tidus747/Adap_multicamara_NJTX2/Array_captures/Scene_5/CAM4_playmobil.jpg

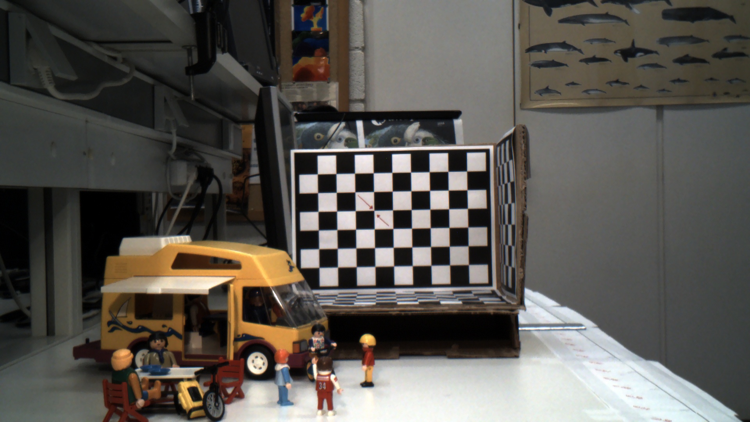
Array_captures/Scene_5/CAM4_playmobil.jpg
