tidus747/Adap_multicamara_NJTX2/Array_captures/Scene_5/Estereo.png

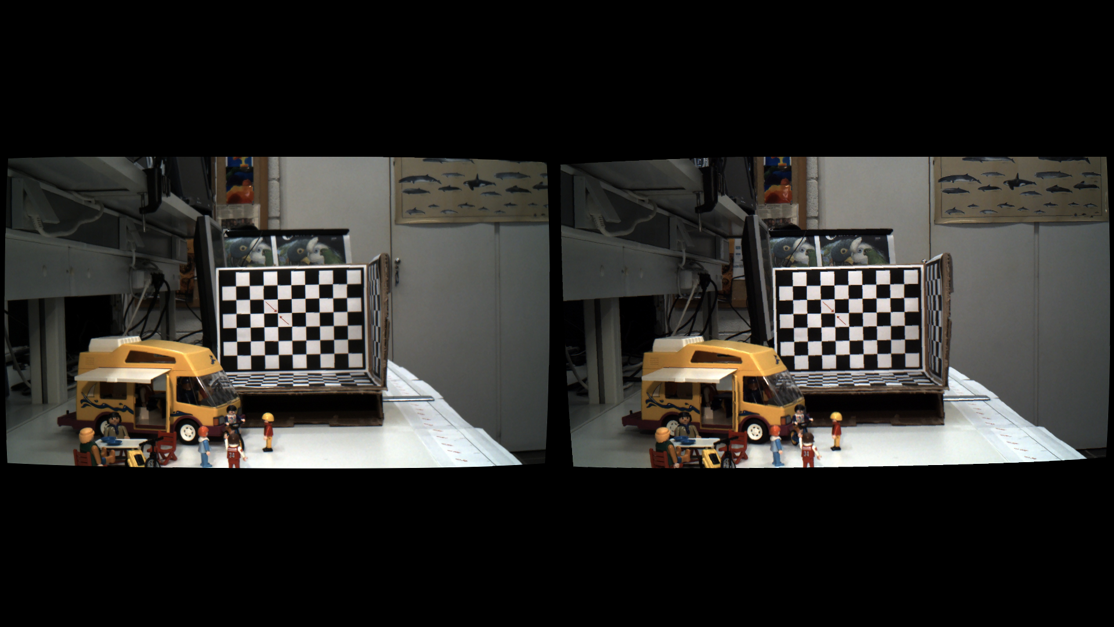
Array_captures/Scene_5/Estereo.png
