tidus747/Adap_multicamara_NJTX2/Array_captures/Scene_6/CAM0_playmobil-2.jpg

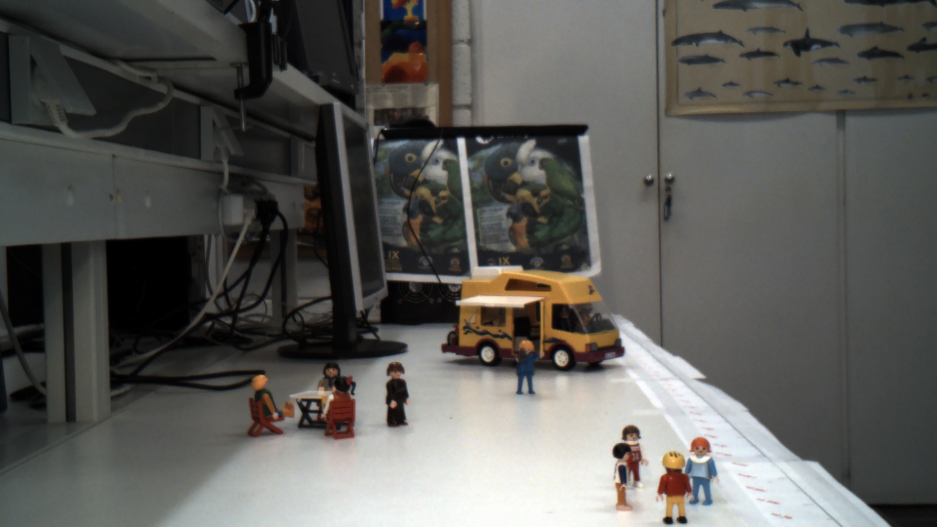
Array_captures/Scene_6/CAM0_playmobil-2.jpg
