tidus747/Adap_multicamara_NJTX2/Array_captures/Scene_8/CAM0_spiderman.jpg

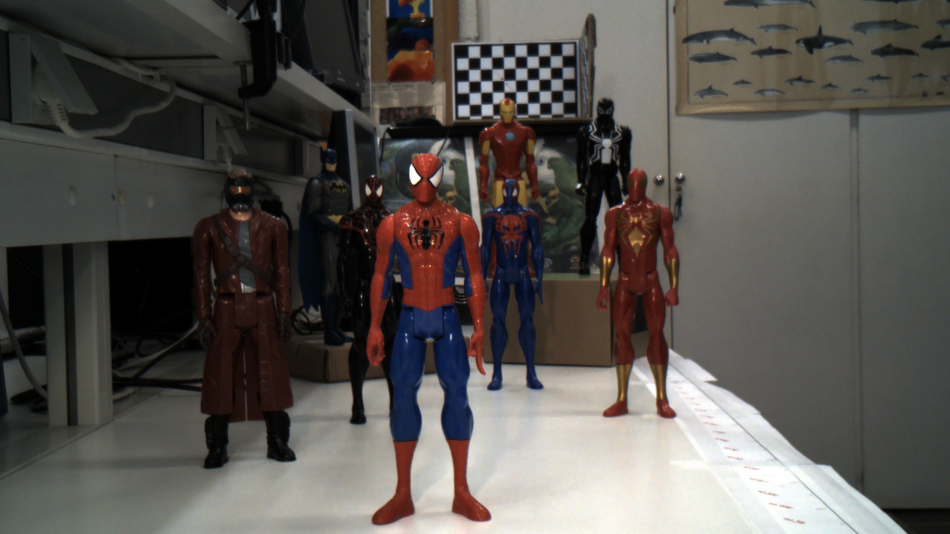
Array_captures/Scene_8/CAM0_spiderman.jpg
