tidus747/Adap_multicamara_NJTX2/Array_captures/Scene_8/CAM3_spiderman.jpg

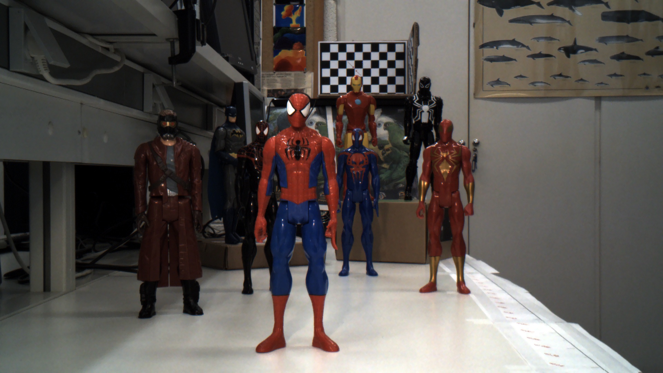
Array_captures/Scene_8/CAM3_spiderman.jpg
