tidus747/Adap_multicamara_NJTX2/Array_captures/Scene_9/CAM0_spiderman-2.jpg

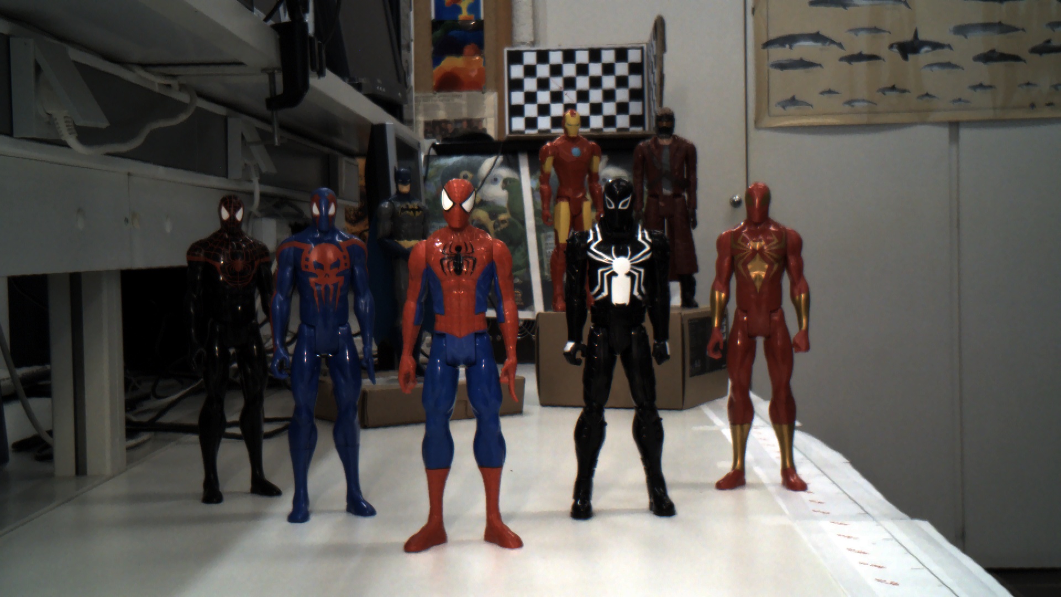
Array_captures/Scene_9/CAM0_spiderman-2.jpg
