tidus747/Adap_multicamara_NJTX2/Desarrollo_Software/Camera_array/Capture_Gstreamer/rejilla.png

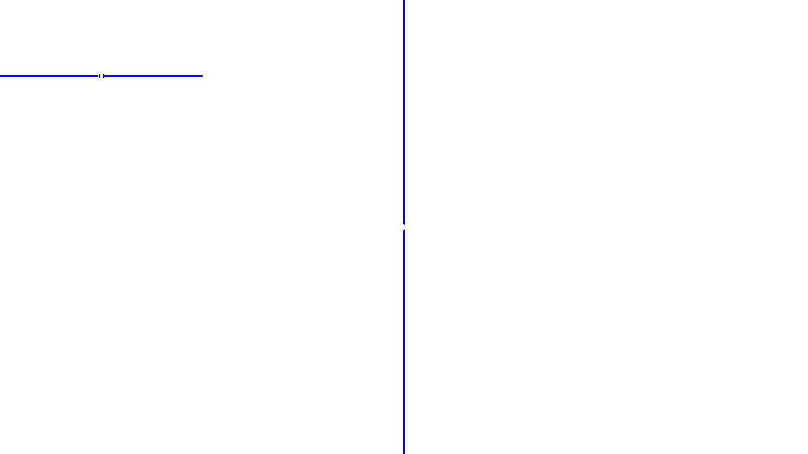
Desarrollo_Software/Camera_array/Capture_Gstreamer/rejilla.png
