tidus747/Adap_multicamara_NJTX2/Desarrollo_Mecanico/Array /Versión V1.1/N10.pdf

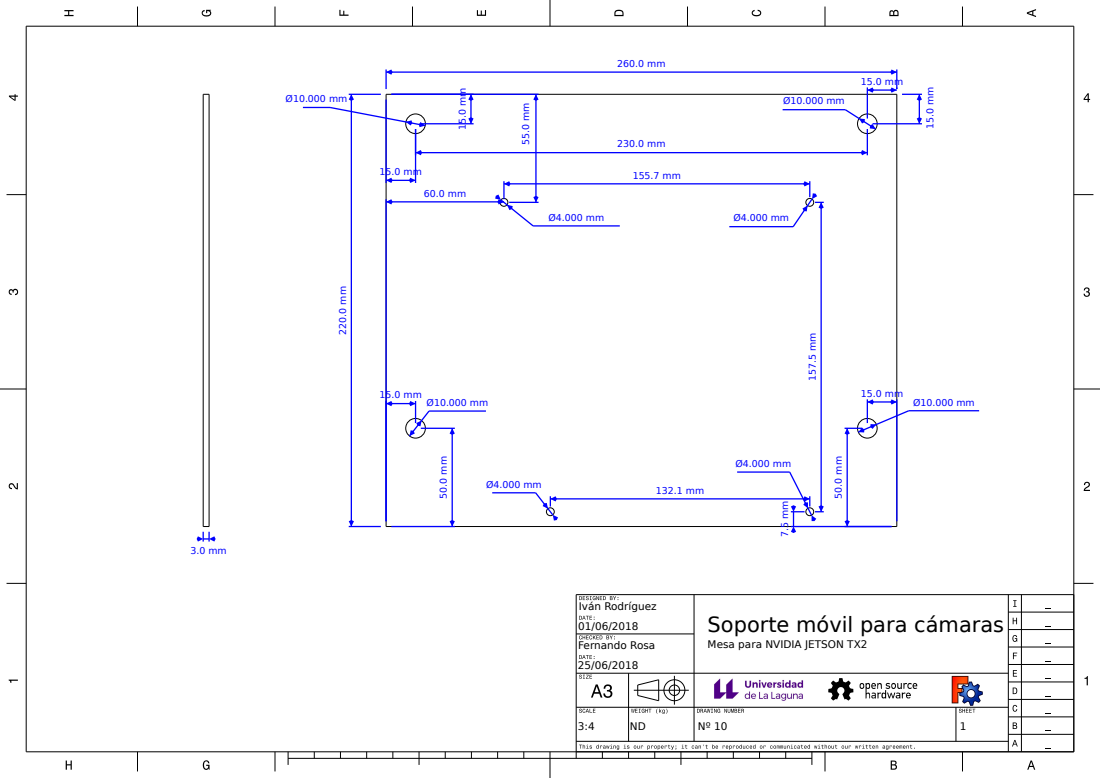
[picture p39: page 1]
Iván Rodríguez; Fernando Rosa

Soporte móvil para cámaras

Mesa para NVIDIA JETSON TX2
