tidus747/Adap_multicamara_NJTX2/Desarrollo_Electronico/Modulo_puente_Raspberry_Camera/Fabricación/Puente_OV5680X1-F.Cu.pdf

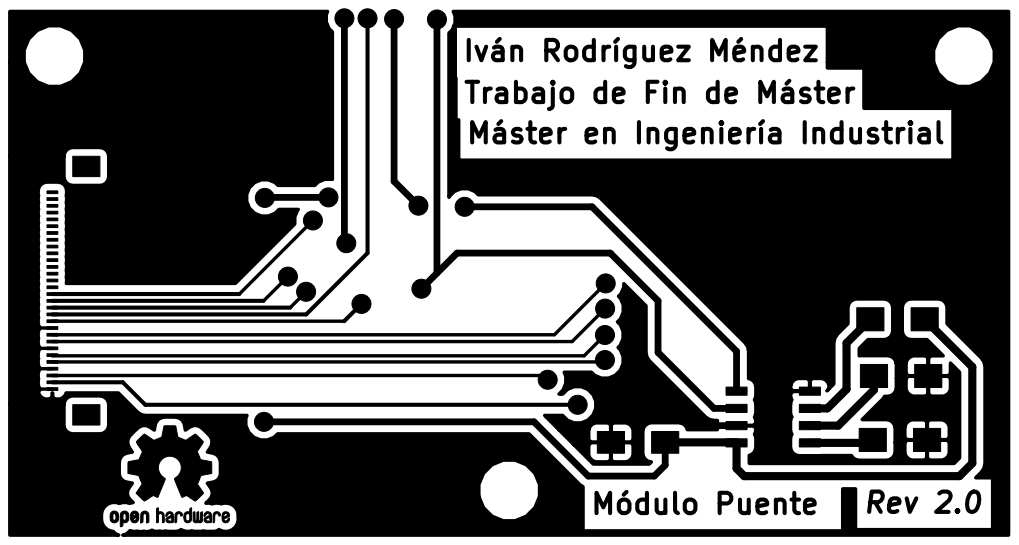
[picture p58: page 1]
