tidus747/Adap_multicamara_NJTX2/Desarrollo_Electronico/Modulo_puente_Raspberry_Camera/PDFs/ACIDO-PUENTE.pdf

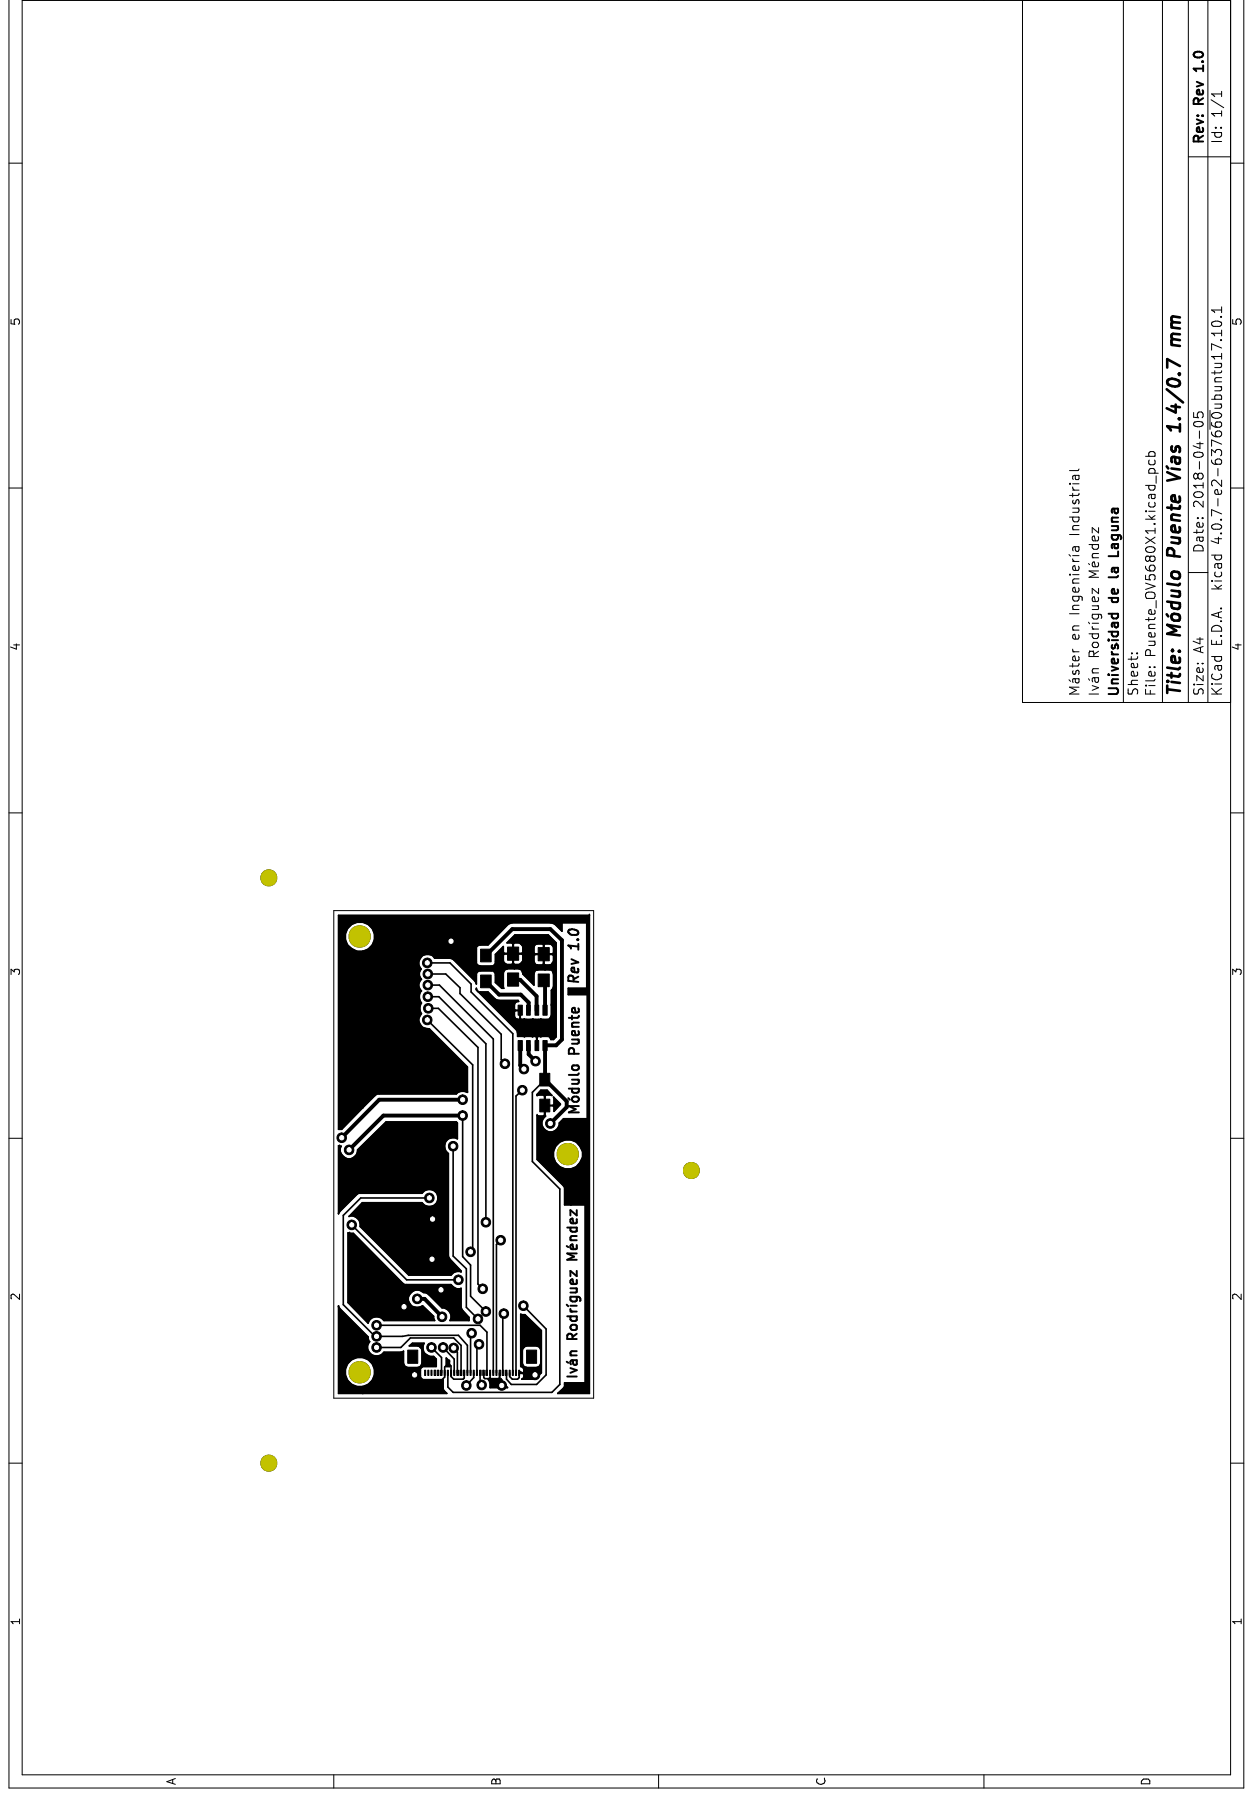
[picture p59: page 1]

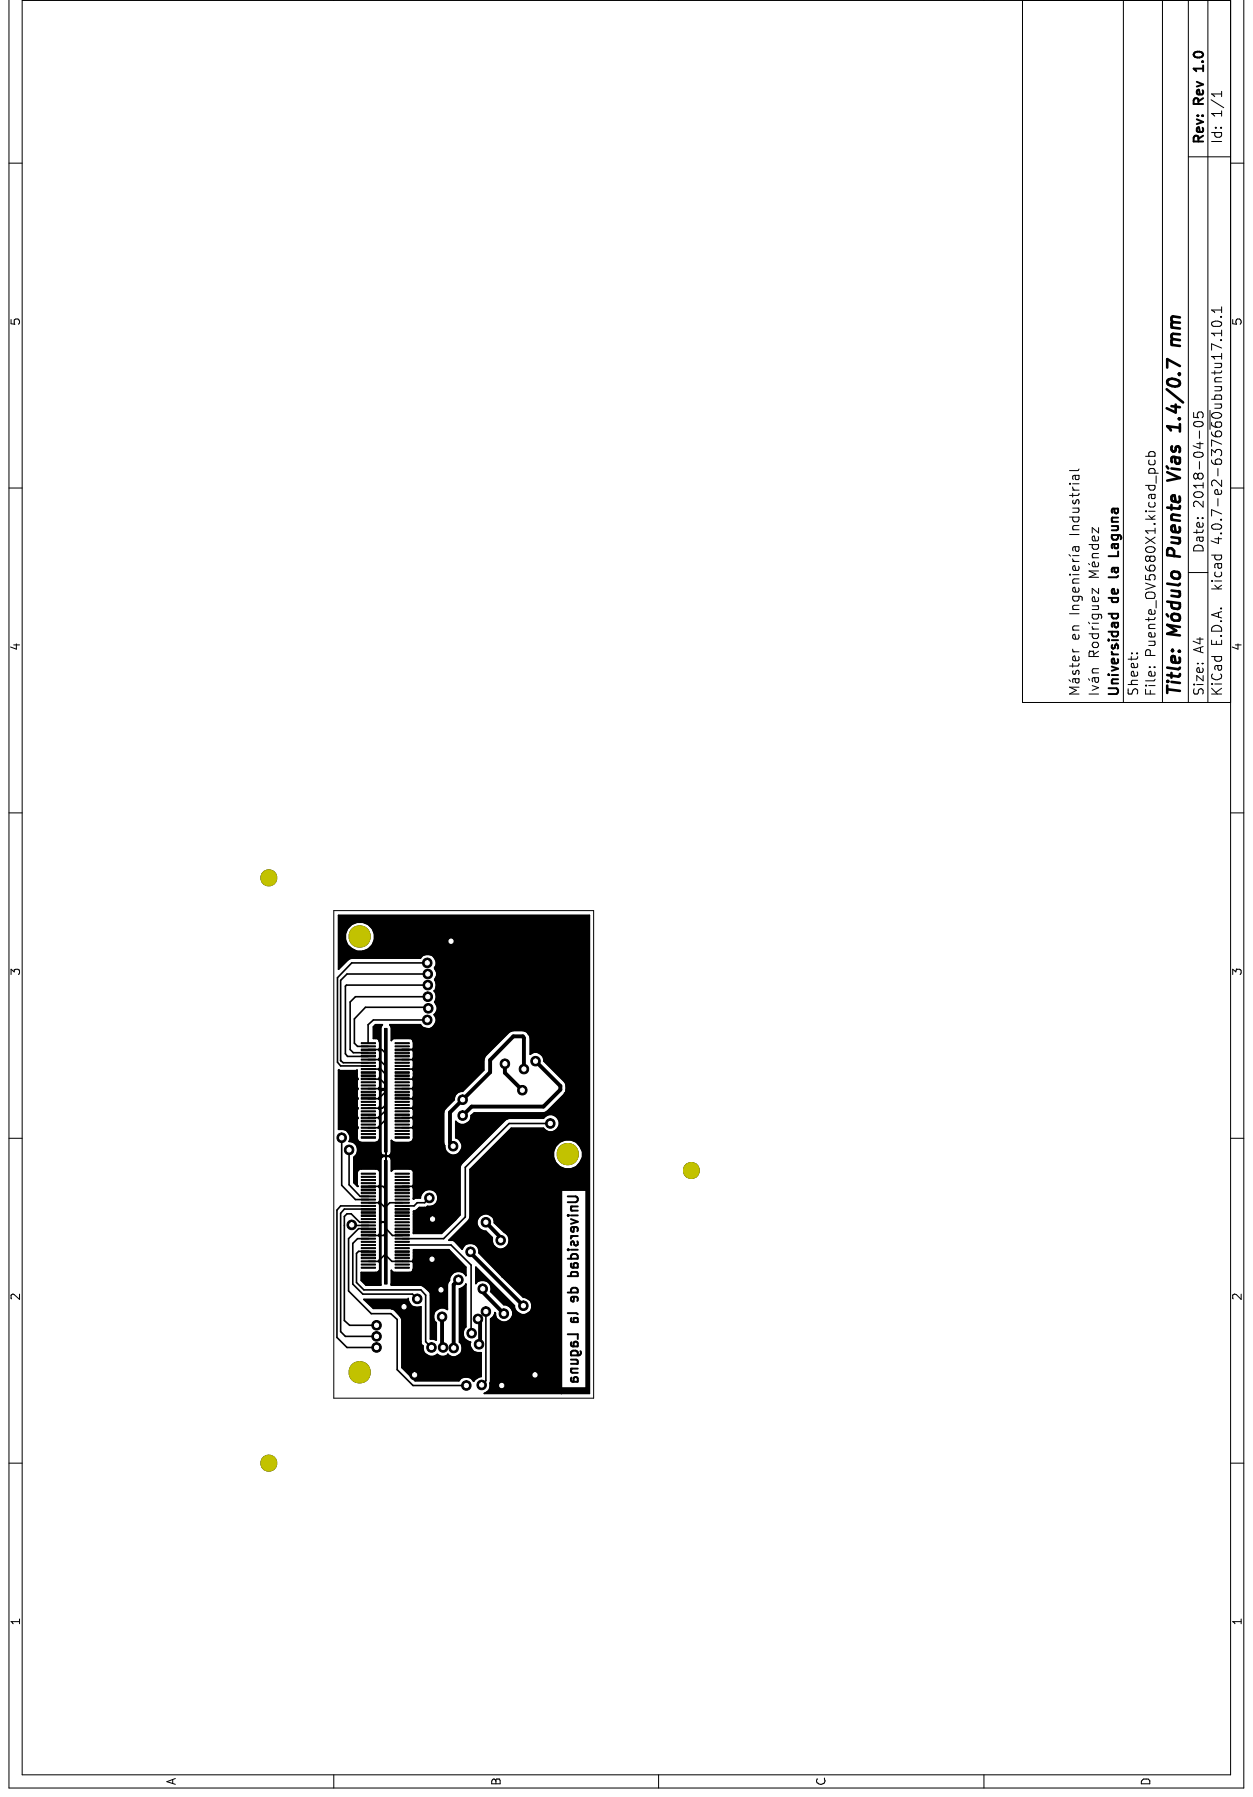
[picture p60: page 2]
