tidus747/Adap_multicamara_NJTX2/Desarrollo_Electronico/Modulo_puente_Raspberry_Camera/PDFs/ACIDO_PUENTE.pdf

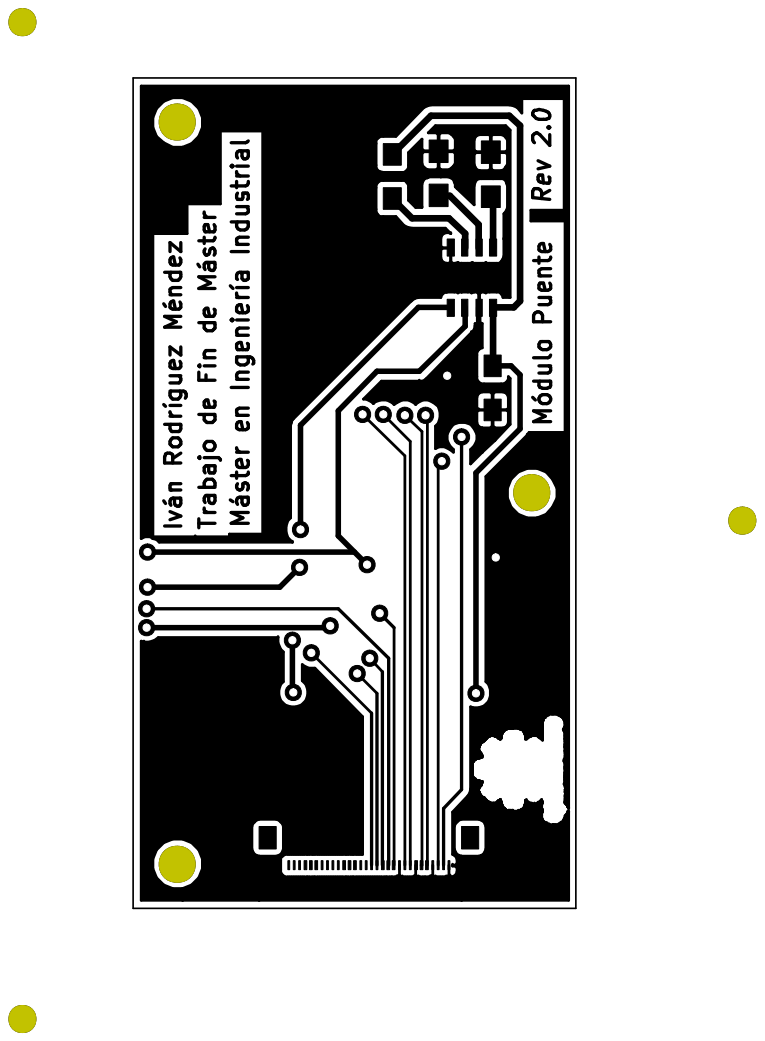
[picture p61: page 1]

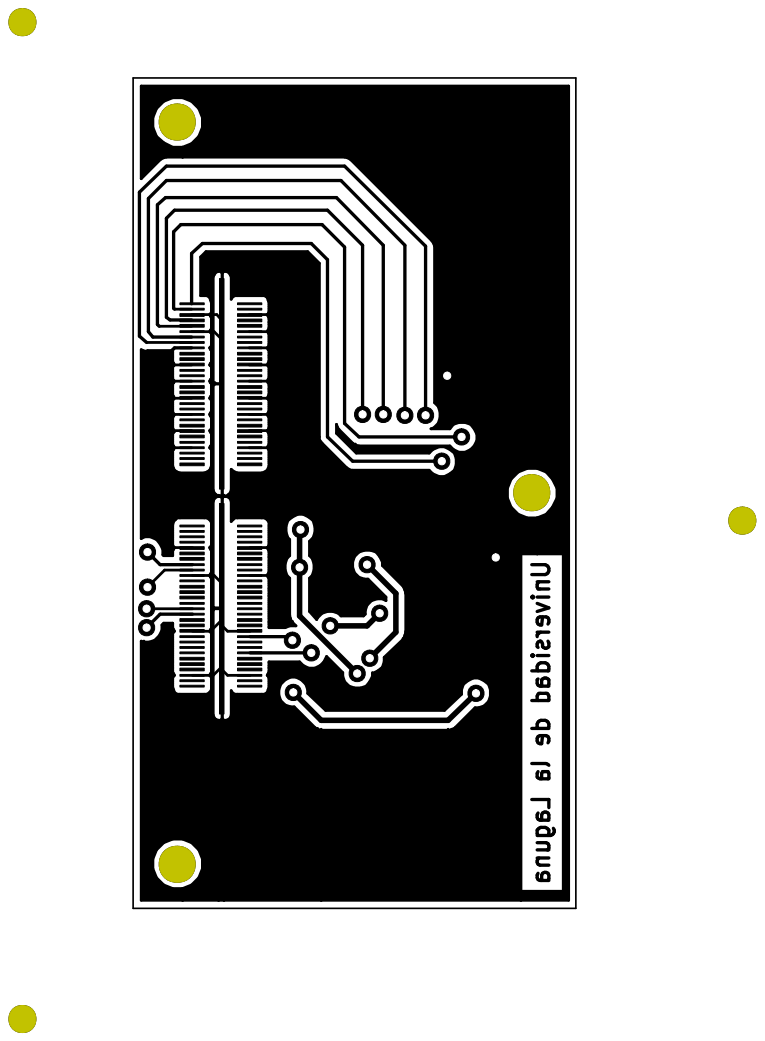
[picture p62: page 2]
