tidus747/Adap_multicamara_NJTX2/Desarrollo_Electronico/Modulo_puente_Raspberry_Camera/PDFs/Planos.pdf

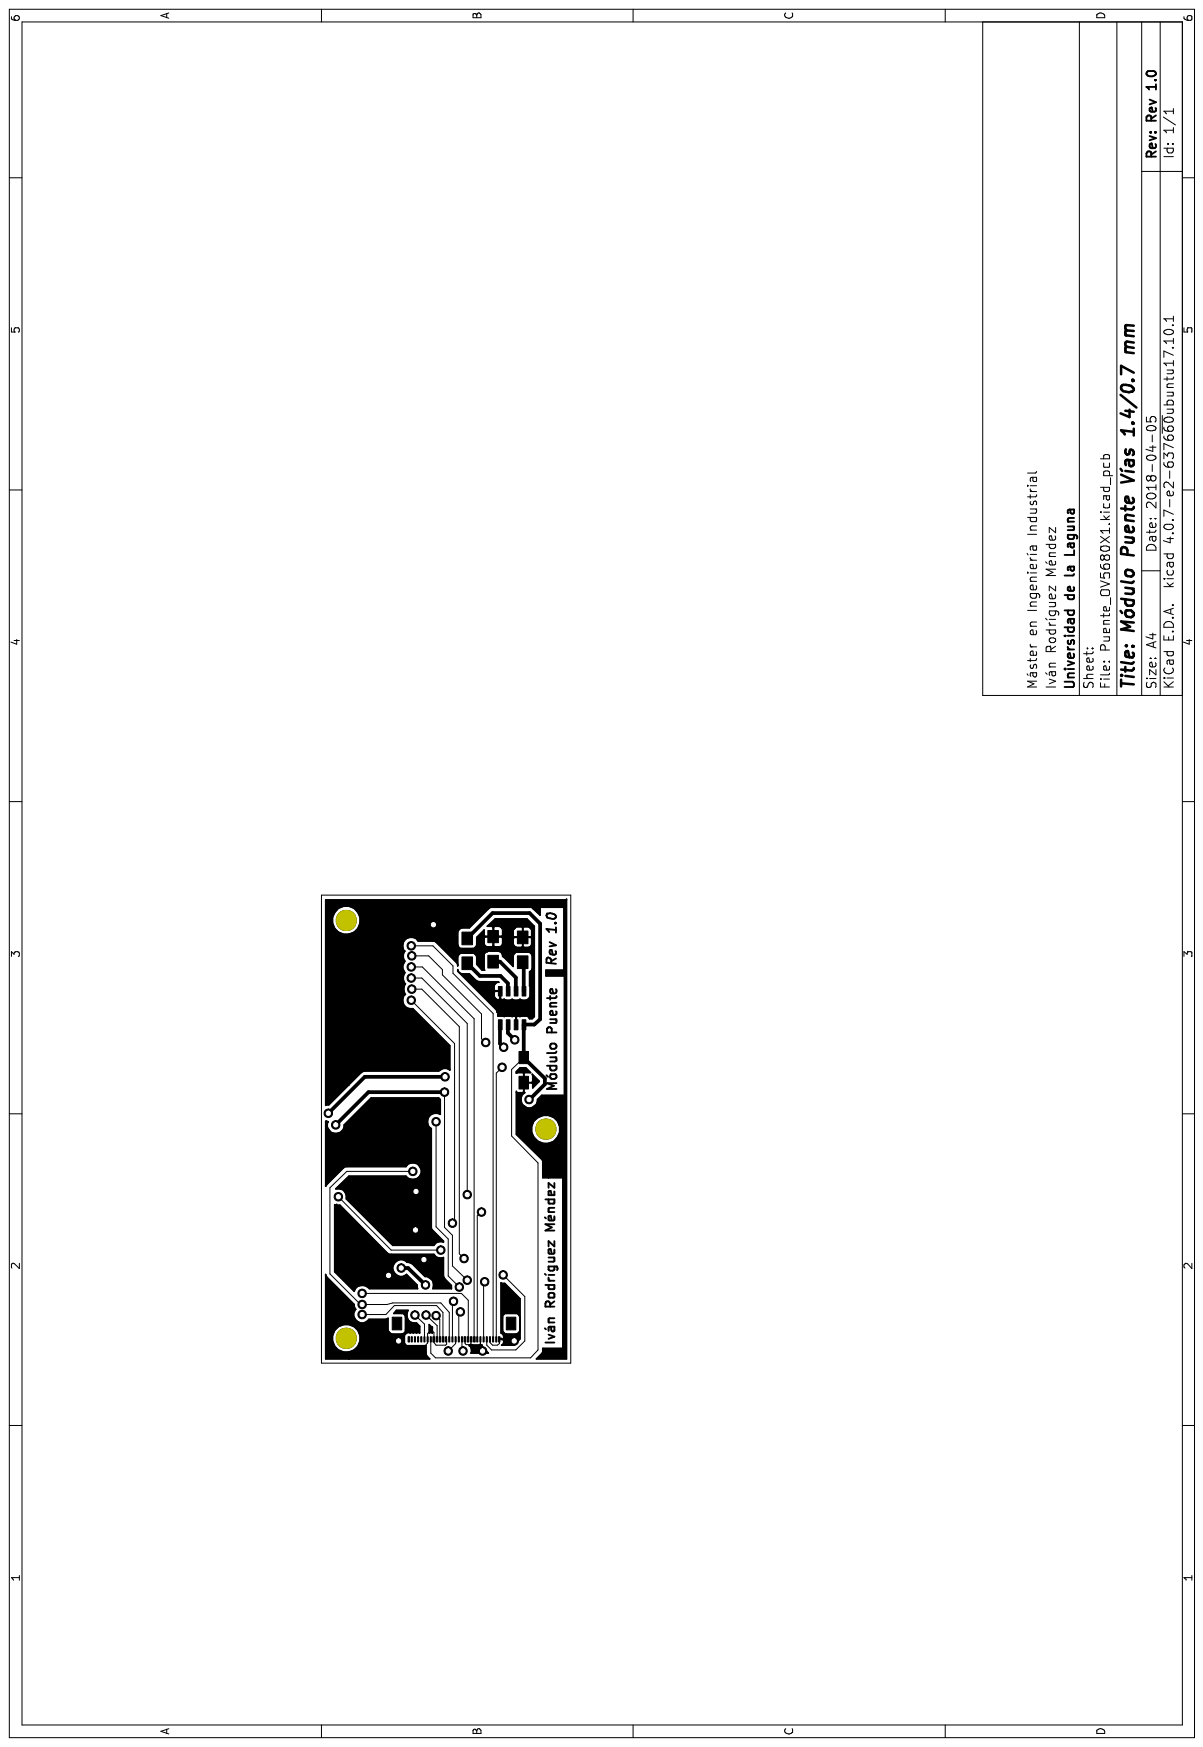
[picture p63: page 1]

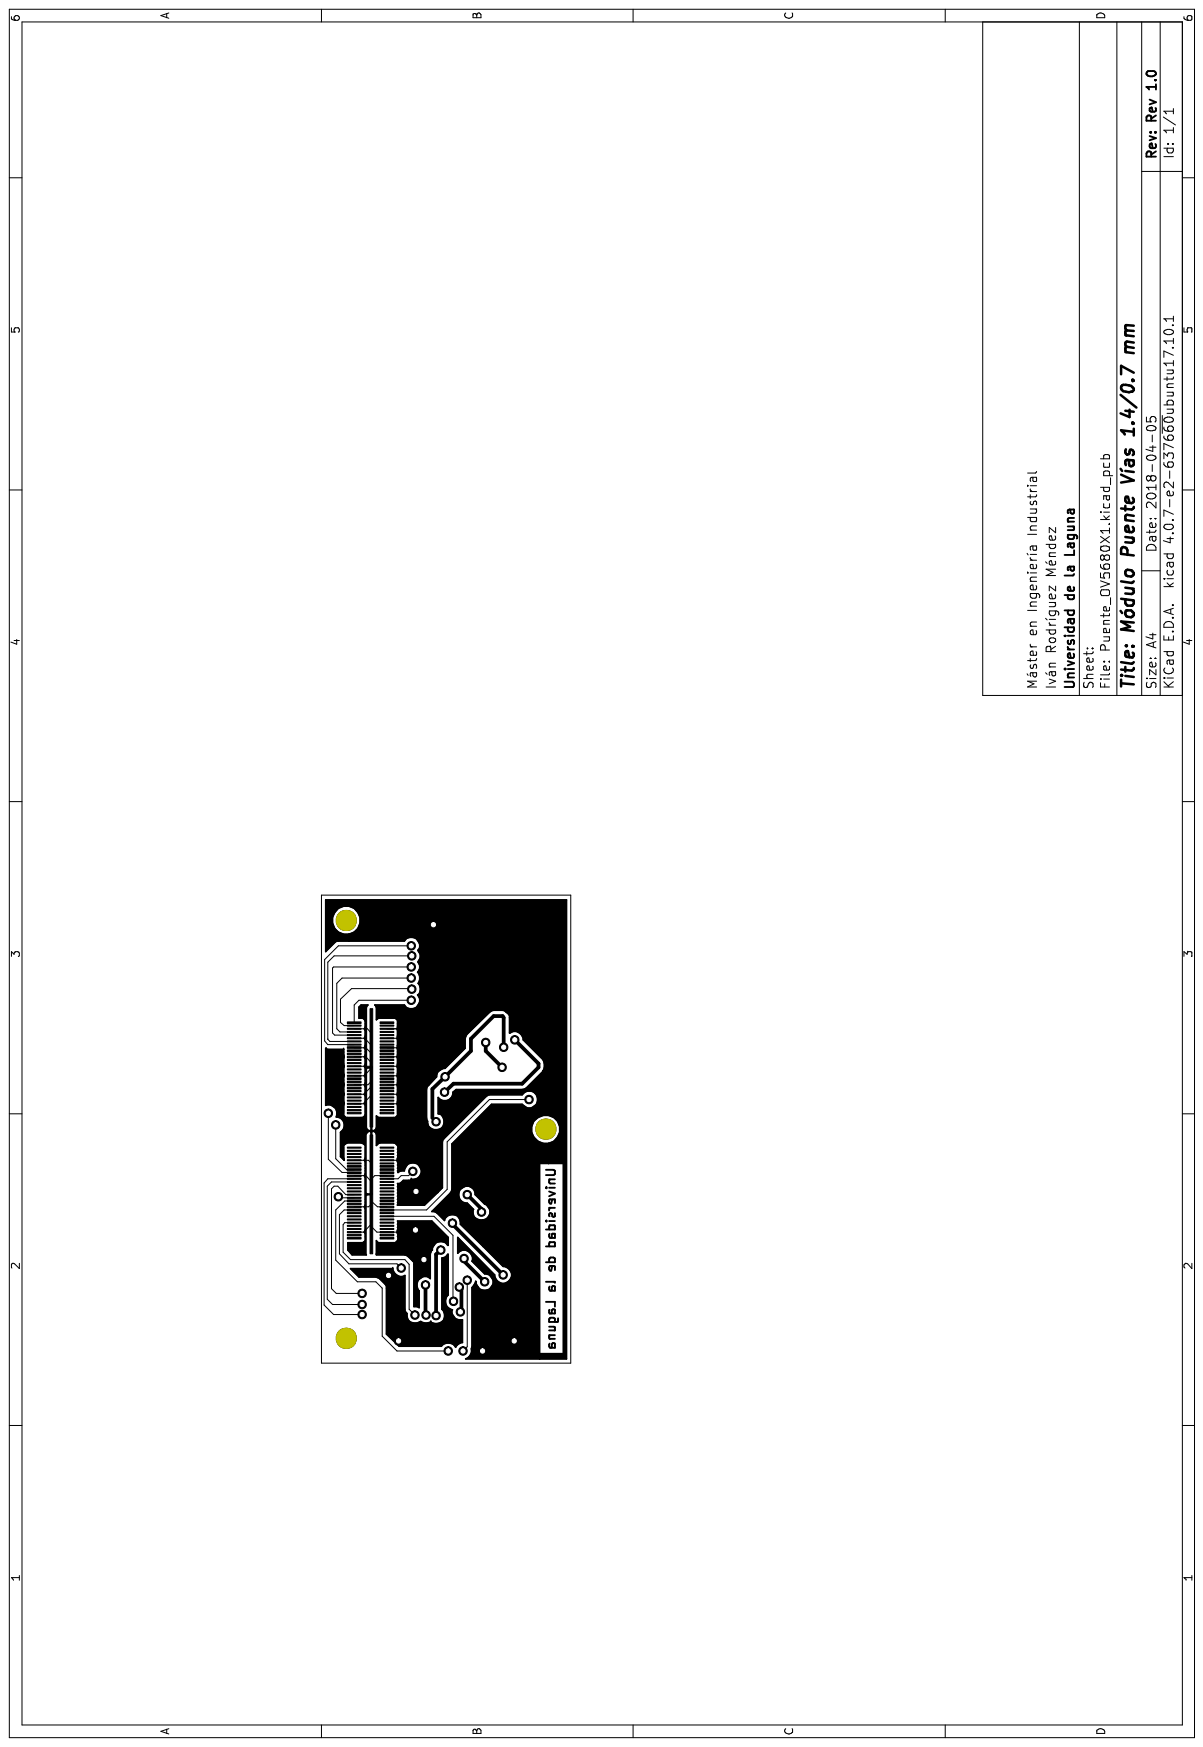
[picture p64: page 2]
