tidus747/Adap_multicamara_NJTX2/Desarrollo_Electronico/Modulo_puente_Raspberry_Camera/PDFs/Puente_OV5647.pdf

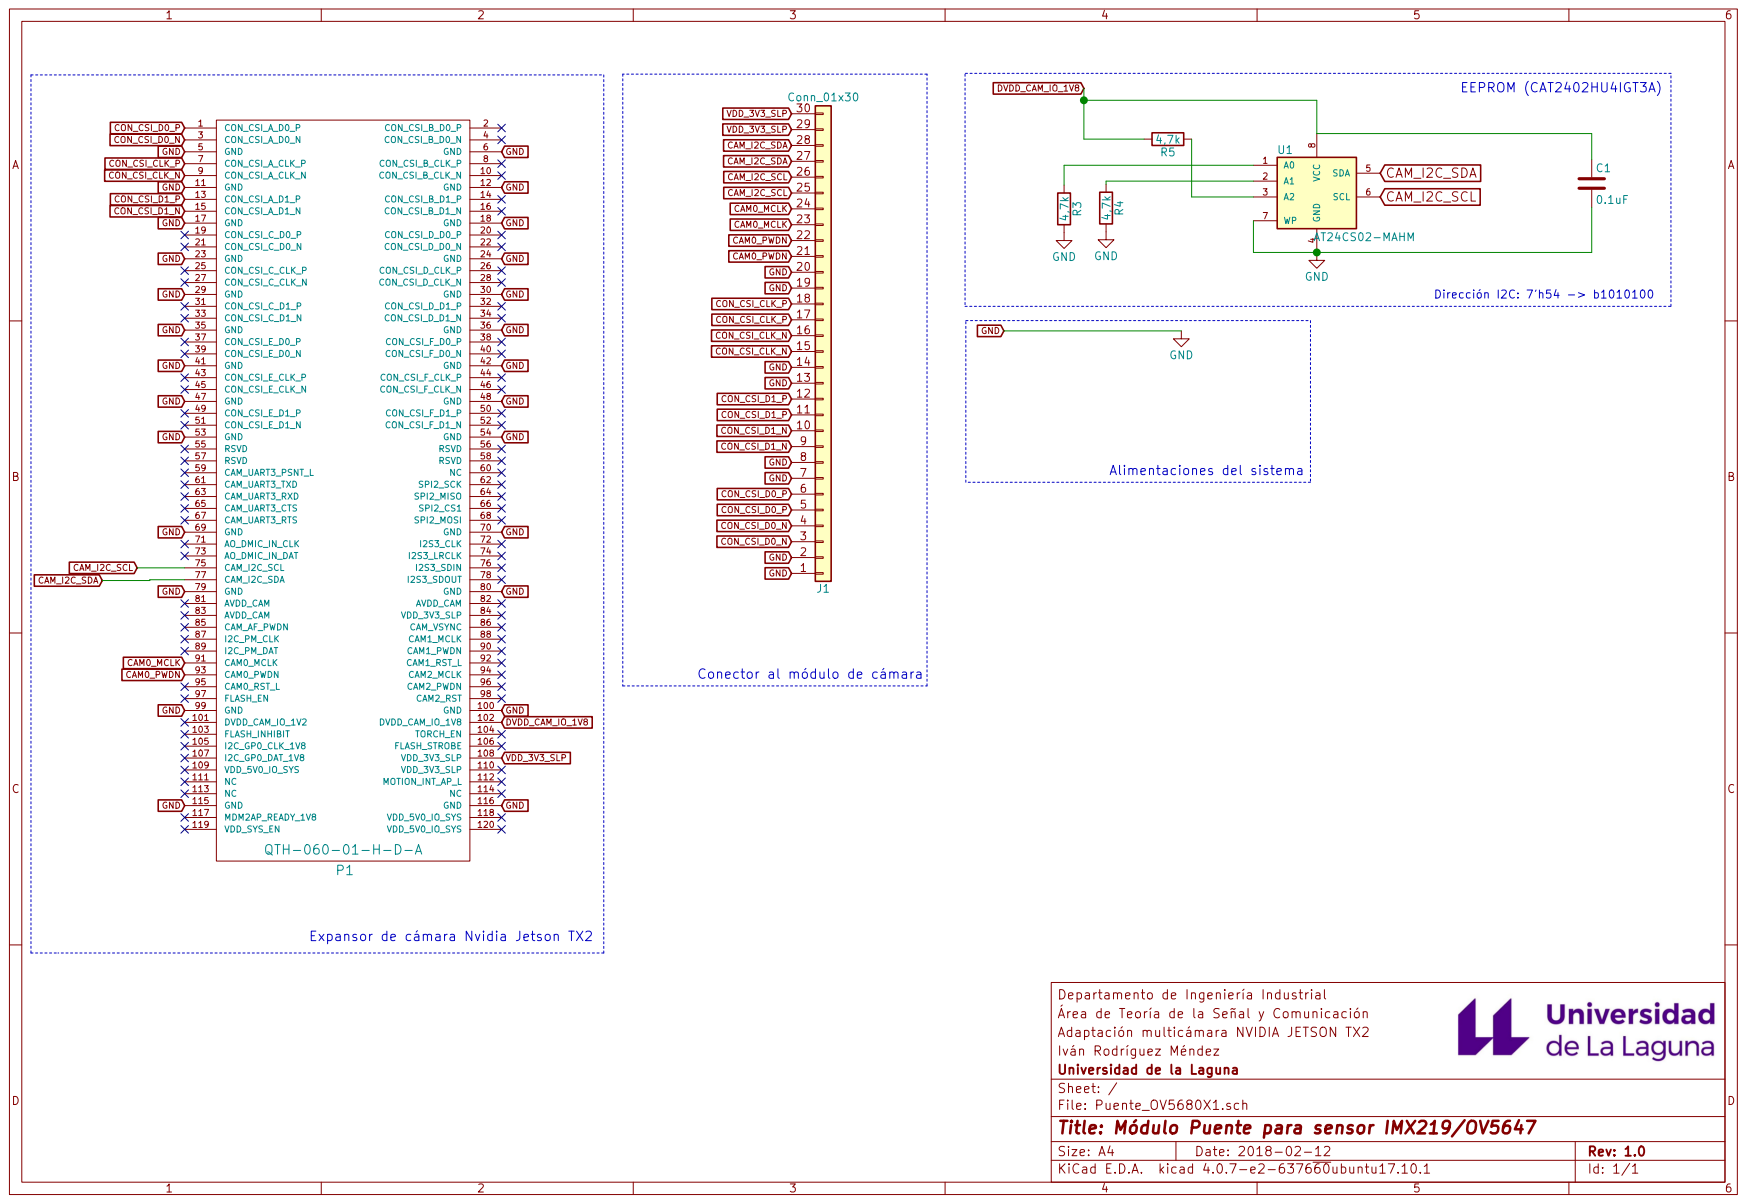
[picture p65: page 1]
