tidus747/Adap_multicamara_NJTX2/Desarrollo_Electronico/Modulo_puente_Raspberry_Camera_Dupont/PDFs/Puente_OV5647_DUPONT.pdf

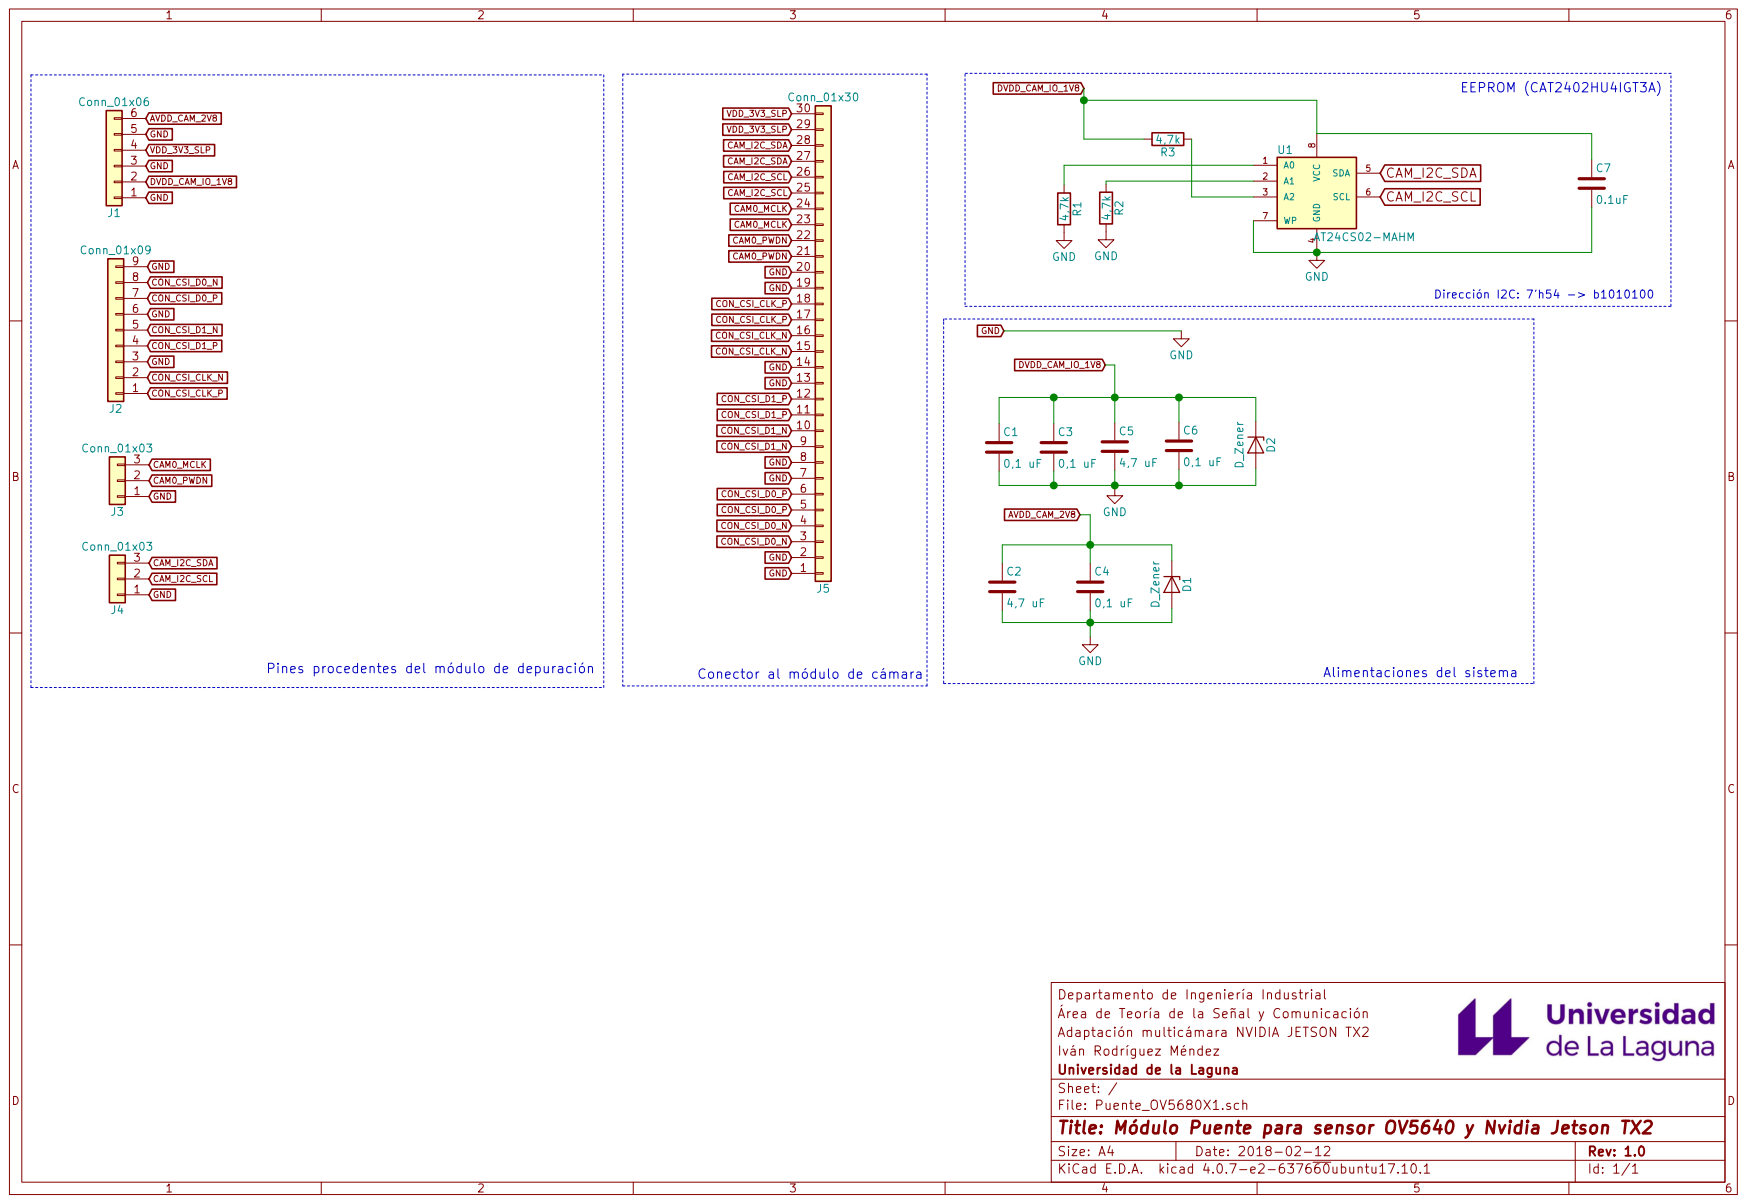
[picture p66: page 1]
