tidus747/Adap_multicamara_NJTX2/Desarrollo_Electronico/Modulo_puente_Raspberry_Camera_Dupont_NO_EEPROM/PDFs/Puente_OV5647_DUPONT_NO_EEPROM.pdf

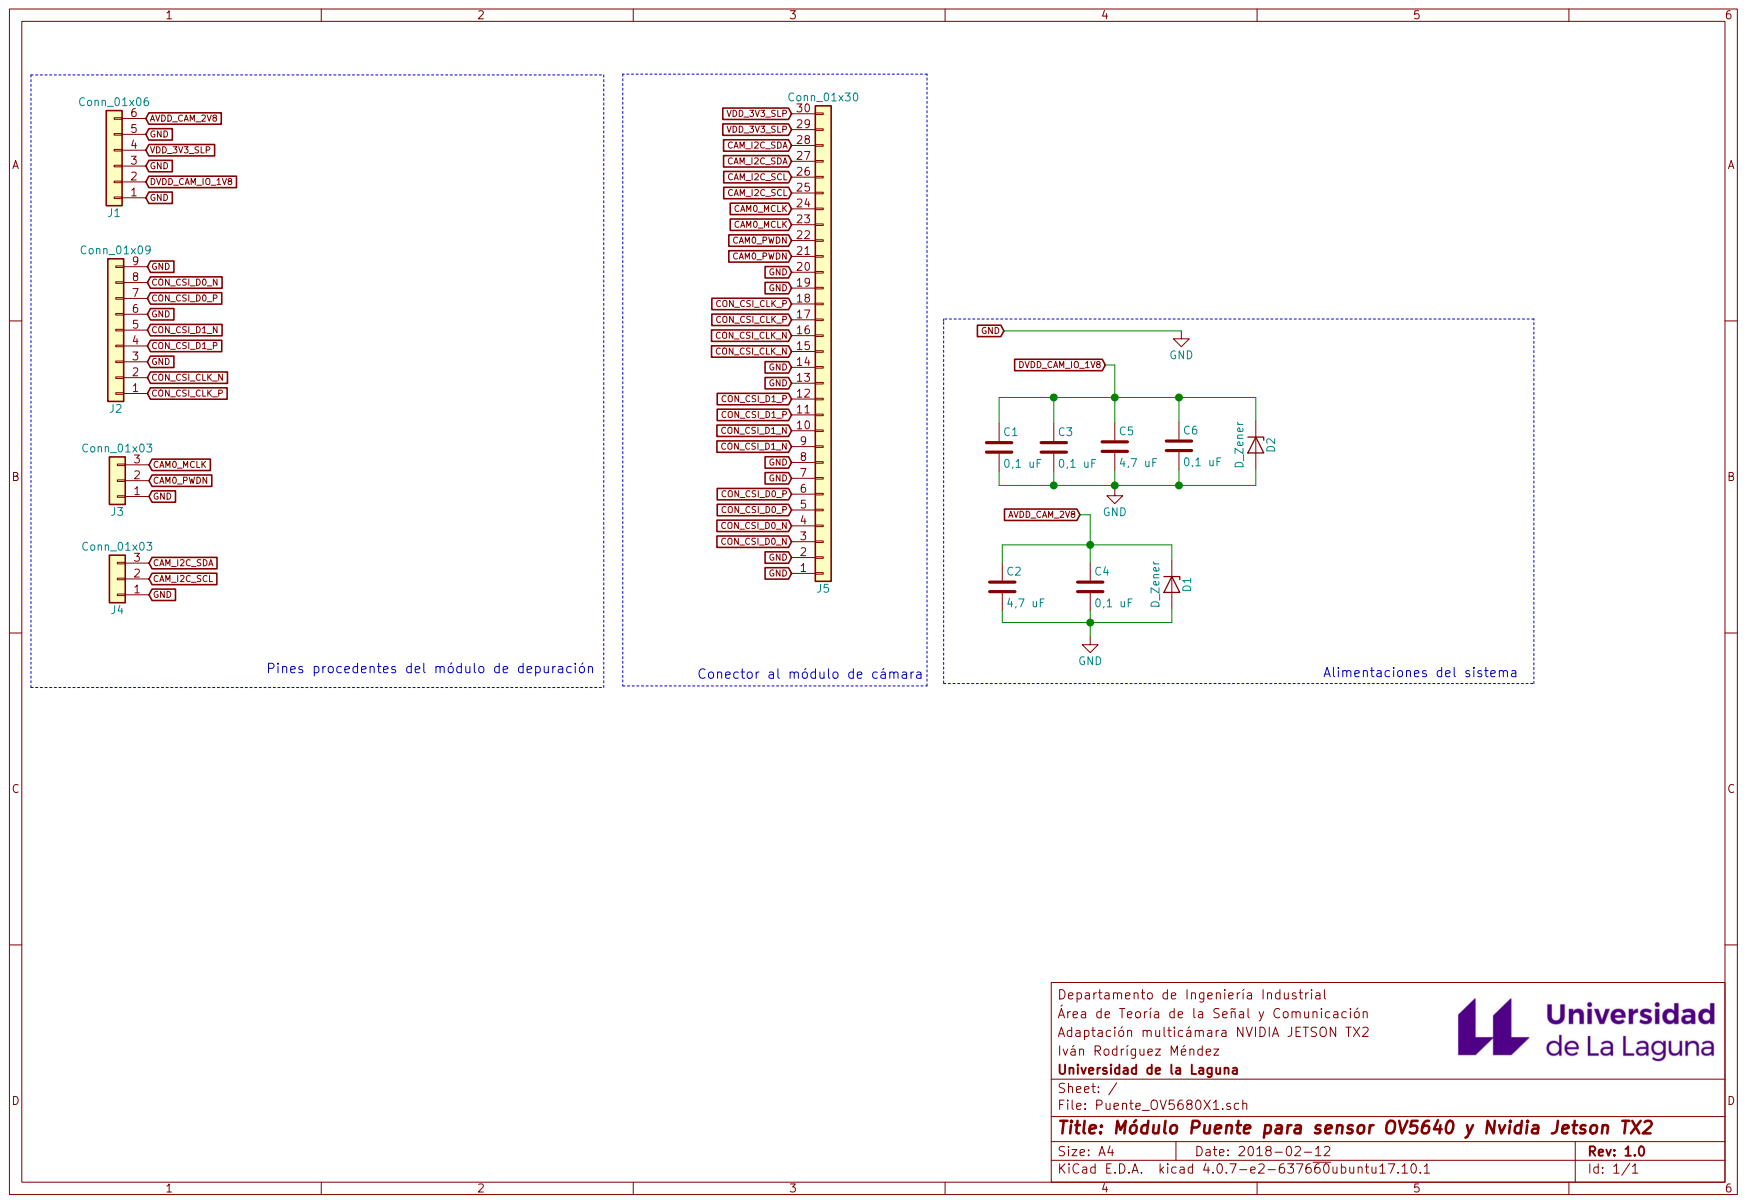
[picture p67: page 1]
