tidus747/Adap_multicamara_NJTX2/Desarrollo_Electronico/Modulo_puente_VIAS_MOD/PDFs/Puente_OV5680X1.pdf

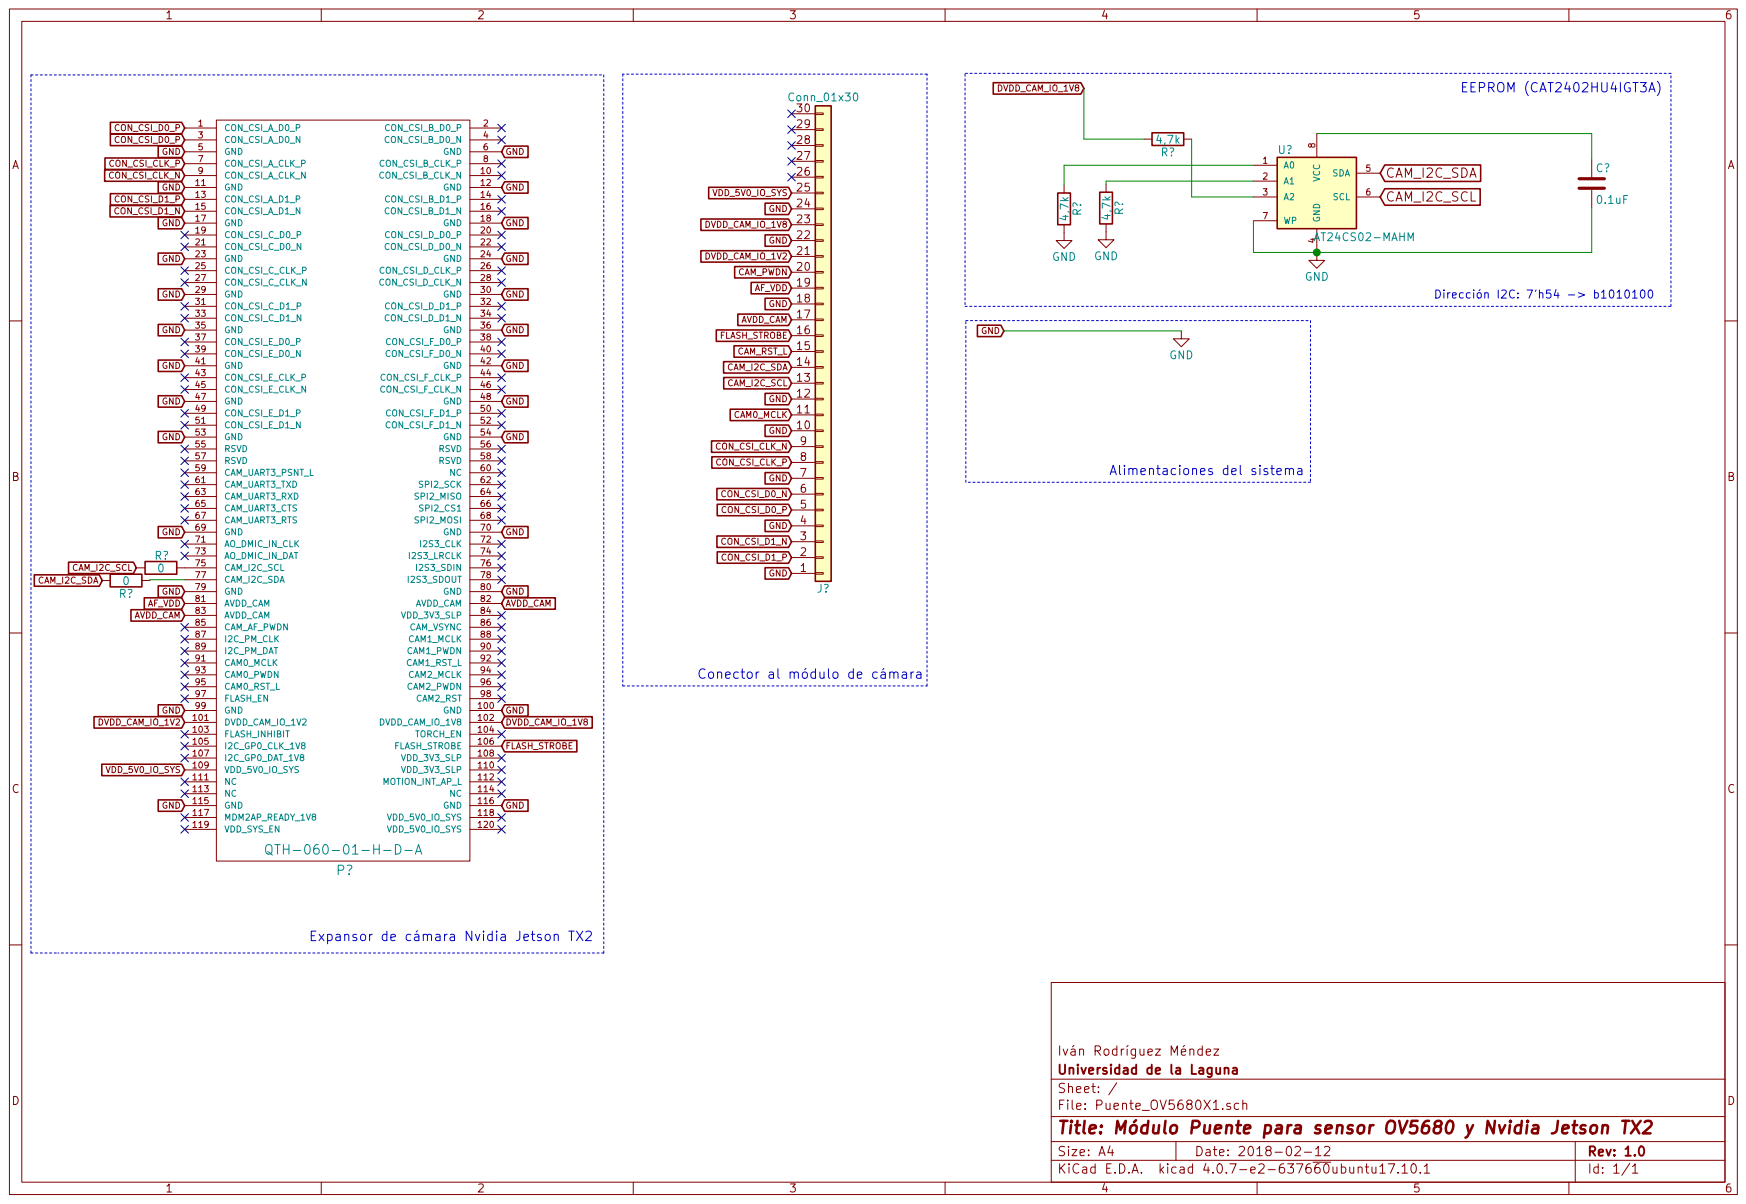
[picture p68: page 1]
