tidus747/Adap_multicamara_NJTX2/Desarrollo_Electronico/Modulo_puente/Fabricación/PDF/Puente_OV5680X1-F.SilkS.pdf

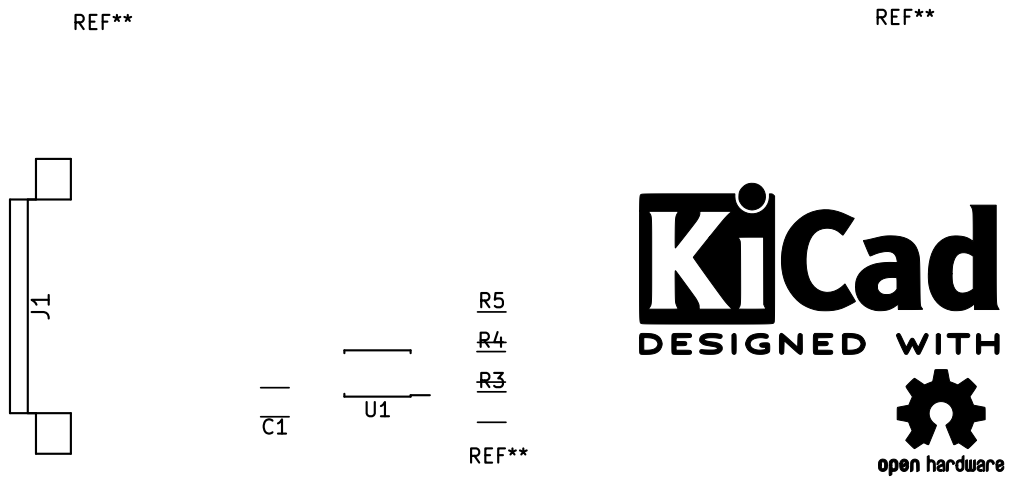
[picture p71: page 1]
