tidus747/Adap_multicamara_NJTX2/Desarrollo_Electronico/Modulo_puente_Raspberry_Camera/Fabricación/SVG/Puente_OV5680X1-Desing.pdf

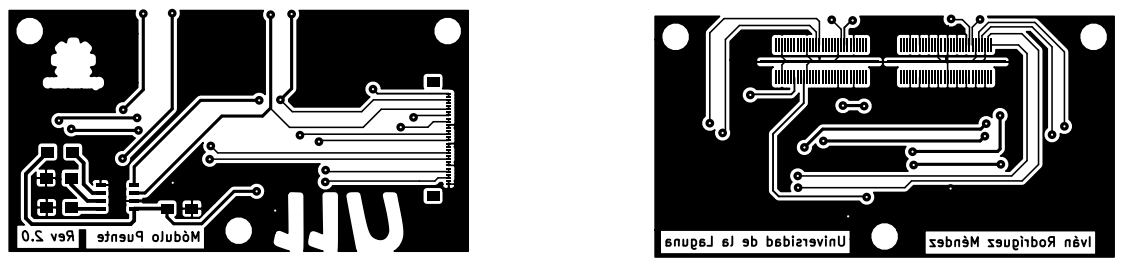
[picture p74: page 1]
