tidus747/Adap_multicamara_NJTX2/Desarrollo_Mecanico/Array /Versión V1.1/N1.pdf

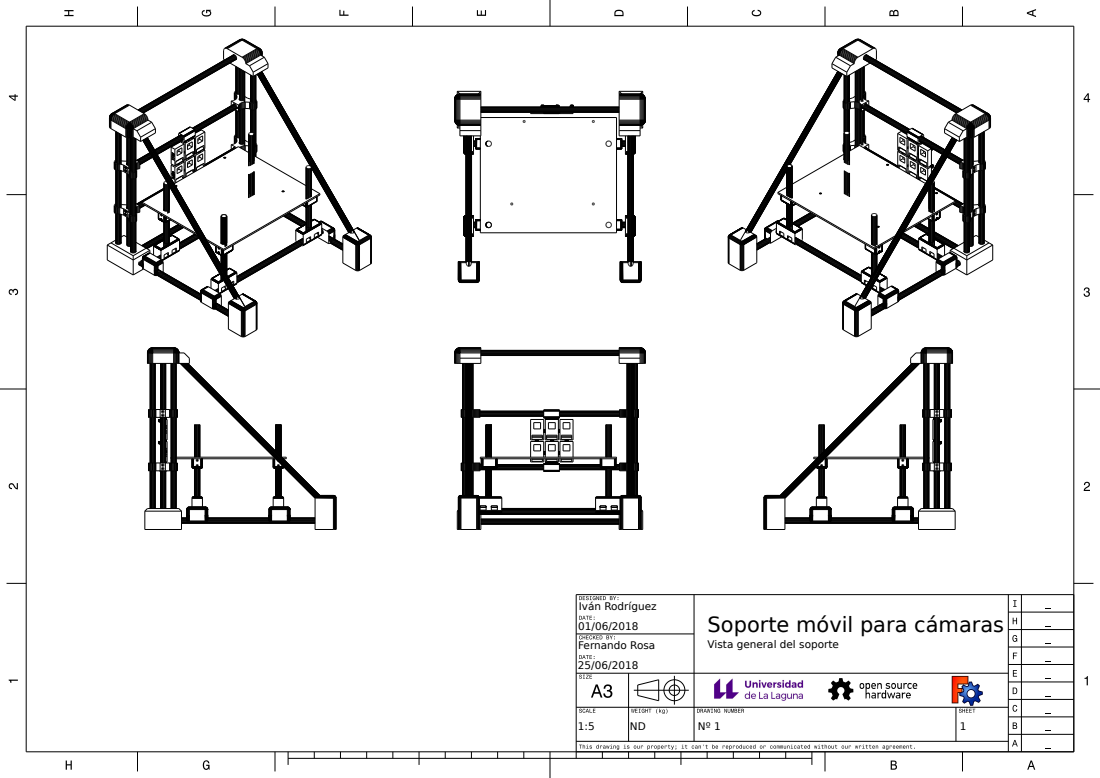
[picture p75: page 1]
Iván Rodríguez; Fernando Rosa

Soporte móvil para cámaras

Vista general del soporte
